cb-embedded/HIP_SecSea/KiCad_src_V1_2/production_preview_reorder_100pcs/res/Checkout.png

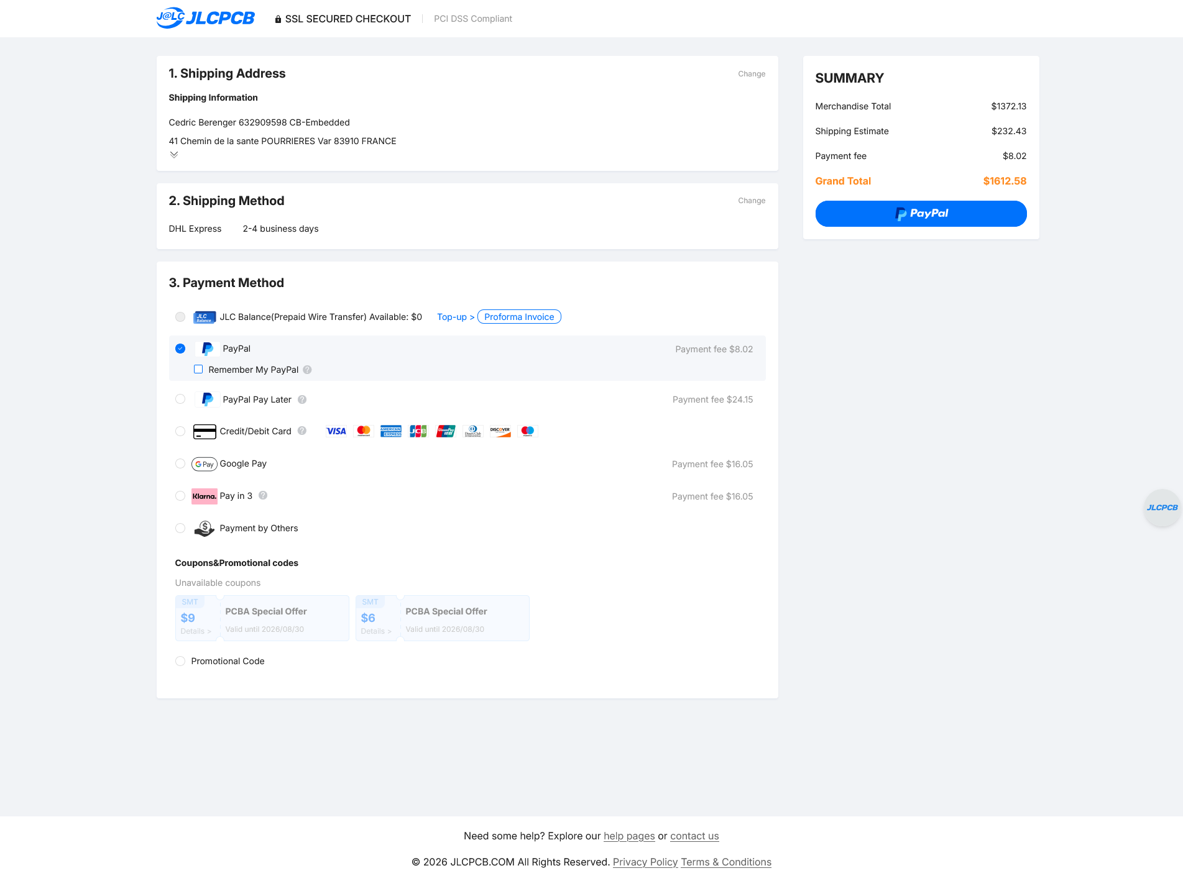
KiCad_src_V1_2/production_preview_reorder_100pcs/res/Checkout.png
