cb-embedded/HIP_SecSea/KiCad_src_V1_2/production_SMT026072760780_PCB_V_1_2/Screenshot 2026-07-27 at 09-27-31 JLCPCB PCBA Viewer.png

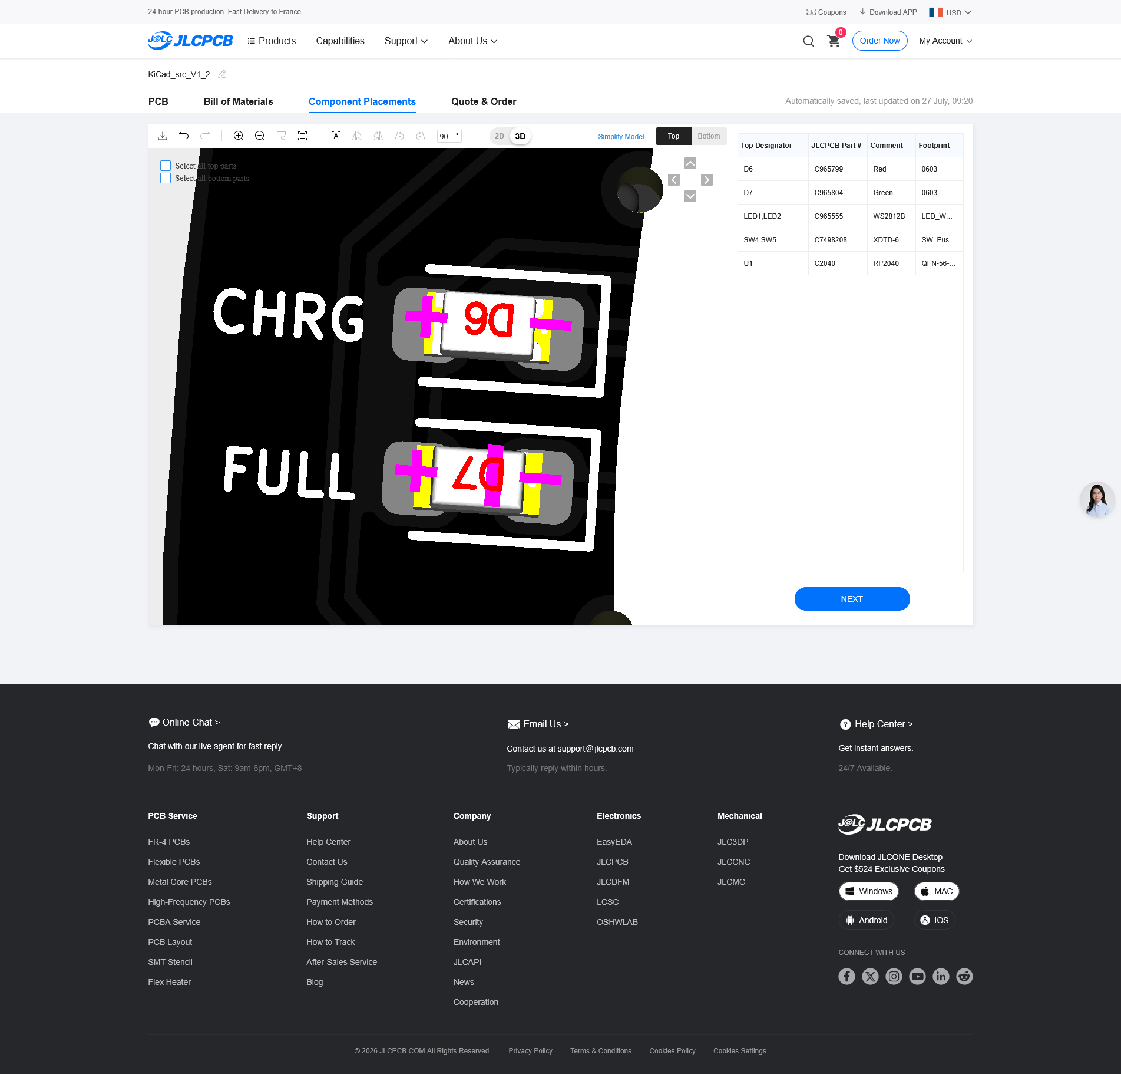
KiCad_src_V1_2/production_SMT026072760780_PCB_V_1_2/Screenshot 2026-07-27 at 09-27-31 JLCPCB PCBA Viewer.png
